santiagoroman/proyectoc21c2018/Simulaciones/Current_Feedback_Amplifier_Protected.asc

C1: cap; 0.3p
C2: cap; 0.3p
C3: cap; 10p
C4: cap; 10p
C5: cap; 470n
C6: cap; 470n
C7: cap; 100n
C8: cap; 100n
C9: cap; 100n
C10: cap; 100n
C11: cap; 470n
C12: cap; 470n
C13: cap; 1000µ
C14: cap; 1000µ
C15: cap; 100n
C16: cap; 100n
Q1: pnp; TIP42C
Q2: npn; BD135
Q3: pnp; BD136
Q4: npn; BC549
Q5: npn; BC549
Q6: pnp; BC559
Q7: pnp; BC559
Q8: pnp; BC559
Q9: npn; BC549
Q10: npn; BC549
Q11: npn; BC549
Q12: npn; BC549
Q13: pnp; BC559
Q14: pnp; BC559
Q15: pnp; BC559
Q16: npn; BC549
Q17: npn; BC549
Q18: npn; BC549
Q19: pnp; BD136
Q23: npn; BC549
Q24: pnp; BD136
Q25: npn; BC549
Q26: npn; BC549
Q27: pnp; BC559
Q28: pnp; BC559
Q29: pnp; BC559
Q30: pnp; BC559
Q31: pnp; BC559
Q32: pnp; BC559
Q33: npn; BD135
Q34: npn; TIP41
Q35: pnp; BC559
Q36: pnp; BC559
Q37: npn; BC549
Q38: npn; BC549
Q39: npn; BC549
Q40: pnp; BC559
QP1: npn; BD135
R1: res; 200
R2: res; 200
R3: res; 100
R4: res; 100
R5: res; 150k
R6: res; 3.2k
R7: res; 1k
R8: res; 100
R9: res; 100
R10: res; 150k
R11: res; 200
R12: res; 1k
R13: res; 200
R14: res; 100
R15: res; 330
R16: res; 50
R17: res; 50
R18: res; 100
R19: res; 3.9k
R20: res; 100
R21: res; 100
R22: res; 100k
R23: res; 100k
R24: res; 330
R25: res; 100
R26: res; 100
R27: res; 5.1
R28: res; 21k
R29: res; 5.1
R30: res; 50
R31: res; 0.5
R32: res; 0.5
R33: res; 50
R34: res; 50
R35: res; 50
R36: res; 10
R37: res; 10
R38: res; 18k
R39: res; 18k
Rcarga: res; 8
RP1: res; 10k
RP1b: res; 10k
RP2: res; 5
RP2b: res; 5
U2: opamp2; TL082
V1: voltage; 30
V2: voltage; 30
V3: signal; SINE(0 1 1k 0 0 0 0); AC 1 0
V4: voltage; 10
V5: voltage; 10
V6: voltage; 5
V7: voltage; 5
Named nets: VCC, 0, VEE, Vin+, Vout, Vin-, Vtl-, Vtl+, V5+, V5-, Iref1, Iref2
.tran 0 17m 10m 0.01m
;ac dec 100 10m 1G
.lib TIP41.lib
.lib BD135.lib
.lib BD136.lib
.lib BC548B.lib
;noise V(Vout) V3 dec 100 10 20k
.lib BC549.lib
.lib BC559.lib
;op
.lib TIP42C.lib
;FOUR 1k V(Vin+)
;option plotwinsize=0
;ption noopiter
.lib TL082.lib
