santiagoroman/proyectoc21c2018/Simulaciones/otros/CircuitoCompletoPDE1V1_MED_MARGEN_FASE.asc

C1: cap; 10n
C2: cap; 1
C3: cap; 10p
C4: cap; 10p
C5: cap; 0.47µ
C6: cap; 0.47µ
C7: cap; 10n
C8: cap; 100n
C9: cap; 100n
C10: cap; 100µ
C11: cap; 100µ
L1: ind; 100m
Q1: pnp; TIP42C
Q13: pnp; BC559
Q14: pnp; BC559
Q15: pnp; BC559
Q16: npn; BC549
Q17: npn; BC549
Q18: npn; BC549
Q19: pnp; BC559
Q20: npn; BC549
Q21: pnp; BC559
Q22: npn; BC549
Q24: pnp; BD136
Q33: npn; BD135
Q34: npn; TIP41
Q35: pnp; BC559
Q36: npn; BC549
Q37: npn; BC549
Q38: npn; BC549
Q39: npn; BC549
Q40: pnp; BC559
Q41: pnp; BC559
Q42: pnp; BC559
R1: res; 39
R2: res; 39
R3: res; 400
R4: res; 300
R5: res; 150
R6: res; 100
R7: res; 2.7k
R8: res; 400
R9: res; 300
R10: res; 150
R11: res; 100
R12: res; 1.8k
R13: res; 200
R14: res; 200
R15: res; 270
R16: res; 50
R17: res; 50
R18: res; 1k
R19: res; 5.1k
R20: res; 100
R21: res; 100
R22: res; 100k
R23: res; 100k
R24: res; 10k
R25: res; 200
R26: res; 200
R27: res; 0.33
R28: res; 2.7k
R29: res; 1.8k
R30: res; 0.33
R31: res; 150
R32: res; 150
Rcarga: res; 8
Rref1: res; 18k
T1: npn; BC548B
T2: npn; BC548B
U1: opamp2; TL081
V1: voltage; 30
V2: voltage; 30
V4: signal; SINE(0 1 1k 0 0 0 0); AC 1 0
Named nets: VEE, VCC, 0, Vin-, salida, entrada
;tran 0 10m 0m 0.01m
.ac dec 100 10m 1G
.lib TIP41.lib
.lib BD135.lib
.lib BD136.lib
.lib BC548B.lib
;noise V(Vout) V3 dec 100 10 20k
.lib BC549.lib
.lib BC559.lib
;op
.lib TIP42C.lib
;FOUR 1k V(Vin+)
;option plotwinsize=0
;ption noopiter
.lib TL081.lib
