santiagoroman/proyectoc21c2018/Simulaciones/otros/ejemploruido.asc

Q1: npn; 2N2222
Q2: npn; 2N2222
R1: res; 1K
R2: res; 1K
R3: res; 1K
R4: res; 1K
R5: res; 10k
V1: voltage; 0; AC 10
V2: voltage; {V}
V3: voltage; {-V}
Named nets: 0, -V, +V, OUT-, OUT+
;NOISE V(out+,out-) V1 list 10K
.param V=15
;step oct param R 500 100K 10
This example demonstrates .stepping a global parameter, R, while computing
the noise at a single frequency.  The resultant plot of V(inoise_density) vs. R
shows a minimun noise with a tail resistance around 16kOhms.
This example schematic is supplied for informational/educational purposes only.
;ac dec 100 10 500k
.noise V(out+,out-) V1 dec 100 10 500k
