santiagoroman/proyectoc21c2018/Simulaciones/otros/CircuitoCompletoPseudoDarlington.asc

C1: cap; 0.3p
C2: cap; 0.3p
C3: cap; 0.63p
C4: cap; 0.63p
C5: cap; 820µ
C6: cap; 820µ
Q1: npn
Q2: npn
Q3: npn
Q4: npn
Q5: pnp
Q6: pnp
Q7: pnp
Q8: pnp
Q9: pnp
Q10: npn
Q11: npn
Q12: pnp
Q13: pnp
Q14: pnp
Q15: pnp
Q16: npn
Q17: npn
Q18: npn
Q19: pnp
Q20: npn
Q20A: npn
Q20B: npn
Q21: pnp
Q21A: pnp
Q21B: pnp
Q22: npn
Q23: npn
Q24: pnp
Q25: pnp
Q26: pnp
Q27: pnp
Q28: npn
Q29: npn
Q30: npn
Q31: pnp
Q31A: pnp
Q31B: pnp
Q32: npn
Q32A: npn
Q32B: npn
Q33: npn
Q34: npn
R1: res; 100
R2: res; 100
R3: res; 400
R4: res; 300
R5: res; 150
R6: res; 100
R7: res; 100
R8: res; 400
R9: res; 300
R10: res; 150
R11: res; 200
R12: res; 200
R13: res; 200
R14: res; 200
R15: res; 200
R16: res; 75
R17: res; 75
R18: res; 75
R19: res; 10k
R20: res; 100
R21: res; 100
R22: res; 330K
R23: res; 330K
R24: res; 22K
Rcarga: res; 8
RSET: res; 18k
U1: UniversalOpamp2
V1: voltage; 30
V2: voltage; 30
V3: signal; SINE(0 250m 1K); AC 250m 0
Named nets: VEE, VCC, Vin+, Vin-, 0, Vin-NEGA, Vout
;op
;tran 0 10m 0.1m 1m
.ac dec 100 10m 1G
