santiagoroman/proyectoc21c2018/Simulaciones/otros/EtapaEntradav1.asc

Q1: pnp
Q2: npn
Q3: npn
Q4: npn
Q5: pnp
Q6: pnp
Q7: npn
Q8: pnp
Rref: res; 18k
V1: voltage
V2: voltage
Named nets: 0, IN+, IN-, V+, V-
