santiagoroman/proyectoc21c2018/Simulaciones/otros/EtapaEntradav2.asc

C1: cap; 0.3p
C2: cap; 0.3p
Q1: npn
Q2: npn
Q3: pnp
Q4: pnp
Q5: pnp
Q6: npn
Q7: npn
Q8: npn
Q9: npn
Q10: npn
Q11: npn
Q12: npn
Q13: pnp
Q14: pnp
Q15: pnp
Q16: pnp
Q17: pnp
Q18: pnp
Q19: pnp
Q20: pnp
Q21: npn
Q22: npn
Q23: npn
Q24: pnp
R1: res; 200
R2: res; 200
R3: res; 18k
R4: res; 200
R5: res; 200
R6: res; 100
R7: res; 100
R8: res; 100
R9: res; 100
R10: res; 10k
RL: res; 10k
V1: voltage; 30
V2: voltage; 30
V3: signal
Named nets: VEE, VCC, Vin+, Vin-, 0
;op
.tran 0 10m 1m 0.01m
